sparkfun/Thing_Plus_Dual-Port_Logging_Shield/Firmware/Dual-Port_microSD_Shield/Dual-Port_microSD_Shield_IO.ino

// Dual-Port microSD Shield I2C interrupt routines

// I2C receiveEvent
// ================
void receiveEvent(int numberOfBytesReceived)
{
  if (receiveEventData.receiveEventLength == 0) // Check if we have finished processing the previous event
  {
    if (numberOfBytesReceived > 0) // Check that we received some data (!) (hopefully redundant!)
    {
      receiveEventData.receiveEventRegister = (volatile byte)Wire.read(); // Store the first byte so we know what to do during the next requestEvent
  
      if (numberOfBytesReceived > 1) // Did we receive more than one byte?
      {
        int i;
        for (i = 1; (i < numberOfBytesReceived) && (i < TINY_BUFFER_LENGTH); i++) // If we did, store it
        {
          receiveEventData.receiveEventBuffer[i - 1] = (volatile byte)Wire.read();
        }
        i--;
        receiveEventData.receiveEventBuffer[i] = (volatile byte)0; // NULL-terminate the data
      }
      
      receiveEventData.receiveEventLength = (volatile byte)numberOfBytesReceived;
    }
  }
  else
  {
    if (numberOfBytesReceived > 0) // Check that we received some data (!) (hopefully redundant!)
    {
      for (int i = 0; (i < numberOfBytesReceived) && (i < TINY_BUFFER_LENGTH); i++) // If we did, read and discard
      {
        Wire.read();
      }
    }
  }
}

// I2C requestEvent
// ================
void requestEvent()
{
  switch (receiveEventData.receiveEventRegister)
  {
    case SFE_DUAL_SD_REGISTER_I2C_ADDRESS: // Does the user want to read the I2C address?
      receiveEventData.receiveEventRegister = (volatile byte)SFE_DUAL_SD_REGISTER_UNKNOWN; // Clear the event
      Wire.write(eeprom_settings.i2cAddress);
      break;
    case SFE_DUAL_SD_REGISTER_FIRMWARE_VERSION: // Does the user want to read the firmware version?
      receiveEventData.receiveEventRegister = (volatile byte)SFE_DUAL_SD_REGISTER_UNKNOWN; // Clear the event
      Wire.write(SFE_DUAL_SD_FIRMWARE_VERSION);
      break;
    case SFE_DUAL_SD_REGISTER_DEFAULT_MODE: // Does the user want to read the defaultMode?
      receiveEventData.receiveEventRegister = (volatile byte)SFE_DUAL_SD_REGISTER_UNKNOWN; // Clear the event
      Wire.write(eeprom_settings.defaultMode);
      break;
    case SFE_DUAL_SD_REGISTER_SLEEP:
    case SFE_DUAL_SD_REGISTER_SPI_MODE:
    case SFE_DUAL_SD_REGISTER_SDIO_MODE:
    case SFE_DUAL_SD_REGISTER_UNKNOWN:
    default:
      receiveEventData.receiveEventRegister = (volatile byte)SFE_DUAL_SD_REGISTER_UNKNOWN; // Clear the event
      break;
  }
}
